JacSko/aioRadio/sw/tuner/devicedriver/include/FrequencyTable.h

#pragma once
#include <cstdint>
#include <vector>
#include <utility>

namespace tuner::devicedriver
{

static inline std::vector<std::pair<uint32_t, const char*>> getDABFrequencyTable ()
{
      std::vector<std::pair<uint32_t, const char*>> frequencyTable = {
      { /*  1  174928 MHz */  0x2AB50, /* 0x2AB50 */ "5A " },
      { /*  2  176640 MHz */  0x2B200, /* 0x2B200 */ "5B " },
      { /*  3  178352 MHz */  0x2B8B0, /* 0x2B8B0 */ "5C " },
      { /*  4  180064 MHz */  0x2BF60, /* 0x2BF60 */ "5D " },
      { /*  5  181936 MHz */  0x2C6B0, /* 0x2C6B0 */ "6A " },
      { /*  6  183648 MHz */  0x2CD60, /* 0x2CD60 */ "6B " },
      { /*  7  185360 MHz */  0x2D410, /* 0x2D410 */ "6C " },
      { /*  8  187072 MHz */  0x2DAC0, /* 0x2DAC0 */ "6D " },
      { /*  9  188928 MHz */  0x2E200, /* 0x2E200 */ "7A " },
      { /* 10  190640 MHz */  0x2E8B0, /* 0x2E8B0 */ "7B " },
      { /* 11  192352 MHz */  0x2EF60, /* 0x2EF60 */ "7C " },
      { /* 12  194064 MHz */  0x2F610, /* 0x2F610 */ "7D " },
      { /* 13  195936 MHz */  0x2FD60, /* 0x2FD60 */ "8A " },
      { /* 14  197648 MHz */  0x30410, /* 0x30410 */ "8B " },
      { /* 15  199360 MHz */  0x30AC0, /* 0x30AC0 */ "8C " },
      { /* 16  201072 MHz */  0x31170, /* 0x31170 */ "8D " },
      { /* 17  202928 MHz */  0x318B0, /* 0x318B0 */ "9A " },
      { /* 18  204640 MHz */  0x31F60, /* 0x31F60 */ "9B " },
      { /* 19  206352 MHz */  0x32610, /* 0x32610 */ "9C " },
      { /* 20  208064 MHz */  0x32CC0, /* 0x32CC0 */ "9D " },
      { /* 21  209936 MHz */  0x33410, /* 0x33410 */ "10A" },
      { /* 22  211648 MHz */  0x33AC0, /* 0x33AC0 */ "10B" },
      { /* 23  213360 MHz */  0x34170, /* 0x34170 */ "10C" },
      { /* 24  215072 MHz */  0x34820, /* 0x34820 */ "10D" },
      { /* 25  216928 MHz */  0x34F60, /* 0x34F60 */ "11A" },
      { /* 26  218640 MHz */  0x35610, /* 0x35610 */ "11B" },
      { /* 27  220352 MHz */  0x35CC0, /* 0x35CC0 */ "11C" },
      { /* 28  222064 MHz */  0x36370, /* 0x36370 */ "11D" },
      { /* 29  223936 MHz */  0x36AC0, /* 0x36AC0 */ "12A" },
      { /* 30  225648 MHz */  0x37170, /* 0x37170 */ "12B" },
      { /* 31  227360 MHz */  0x37820, /* 0x37820 */ "12C" },
      { /* 32  229072 MHz */  0x37ED0, /* 0x37ED0 */ "12D" },
      { /*  36  230784 MHz */  0x38580,  /*  0x38580  */  "13A"  },
      { /*  37  232496 MHz */  0x38C30,  /*  0x38C30  */  "13B"  },
      { /*  38  234208 MHz */  0x392E0,  /*  0x392E0  */  "13C"  },
      { /*  39  235776 MHz */  0x39900,  /*  0x39900  */  "13D"  },
      { /*  40  237488 MHz */  0x39FB0,  /*  0x39FB0  */  "13E"  },
      { /*  41  239200 MHz */  0x3A660,  /*  0x3A660  */  "13F"  }};
      return frequencyTable;
}

}
